timwhat/Quartz58/IMGS/cad20250729.png

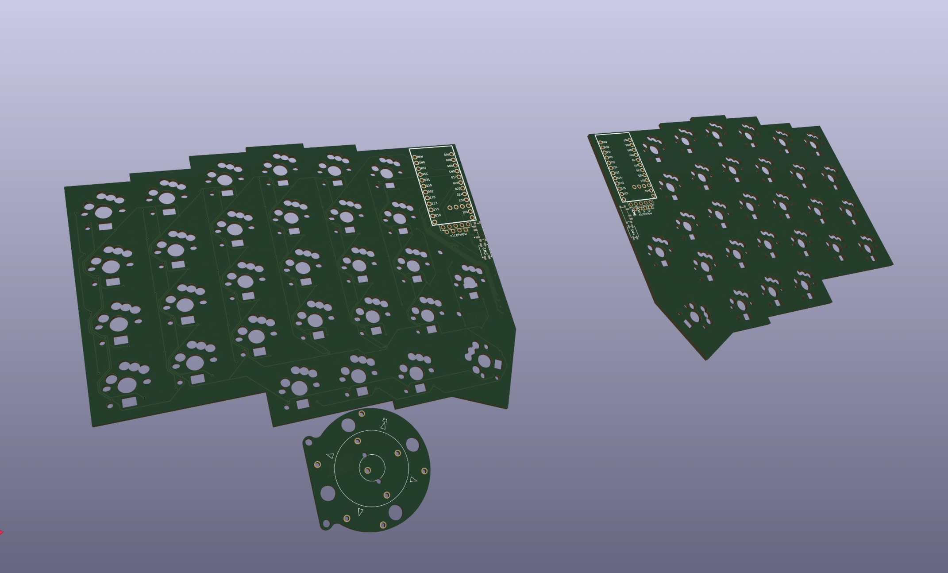
IMGS/cad20250729.png
