timwhat/Quartz58/IMGS/cad20250805.png

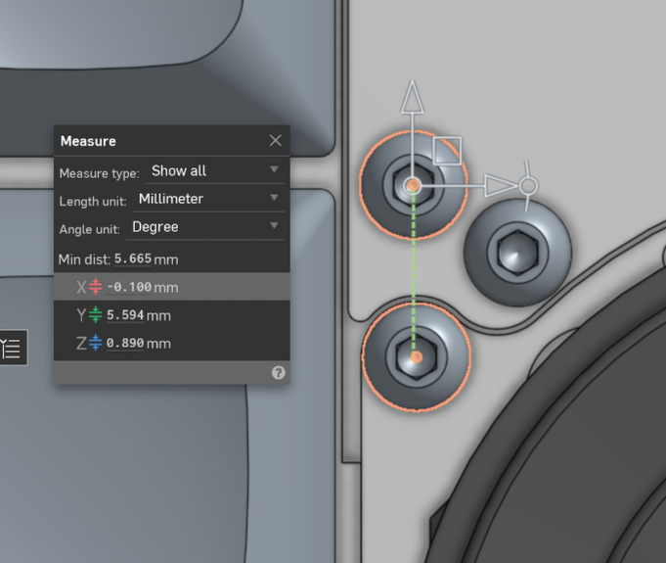
IMGS/cad20250805.png
