timwhat/Quartz58/IMGS/cad20250823pt6.png

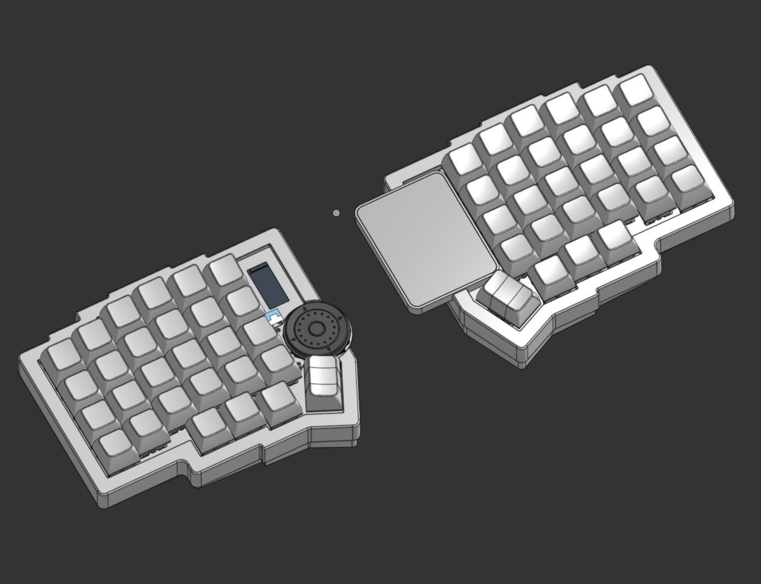
IMGS/cad20250823pt6.png
