timwhat/Quartz58/IMGS/pcb20250806.png

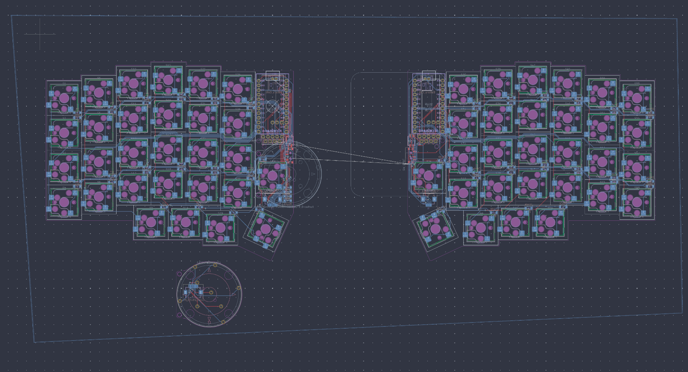
IMGS/pcb20250806.png
