timwhat/Quartz58/IMGS/pcb20250817pt5.png

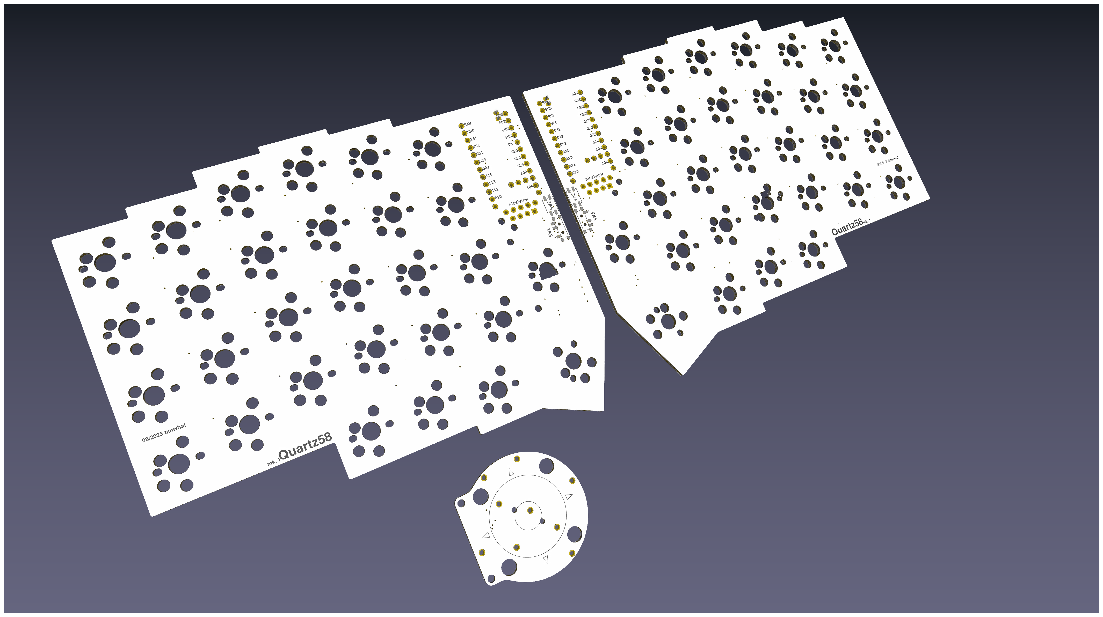
IMGS/pcb20250817pt5.png
